ubilab-ws21/puzzle-4/Firmware/Raspberry/pictures/Achtung.png

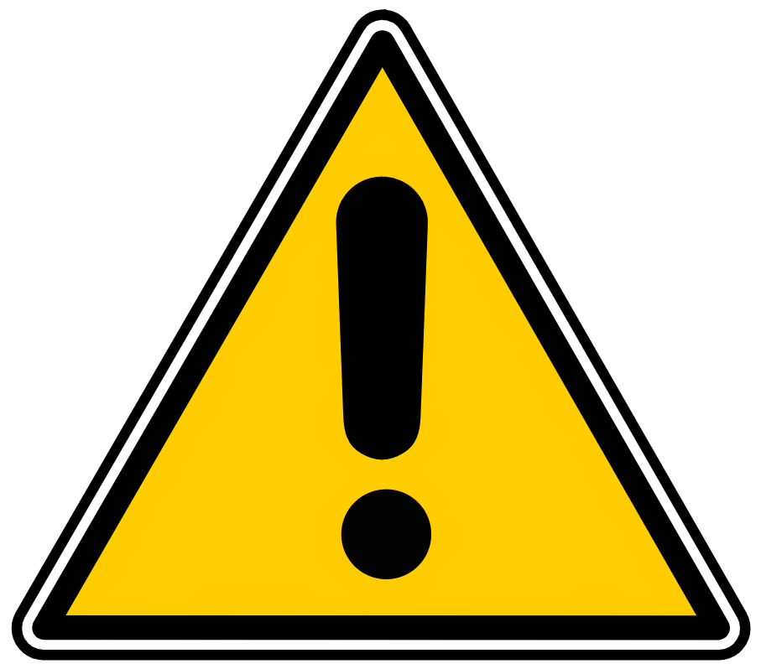
Firmware/Raspberry/pictures/Achtung.png
