ubilab-ws21/puzzle-4/Firmware/Raspberry/pictures/Blitz.png

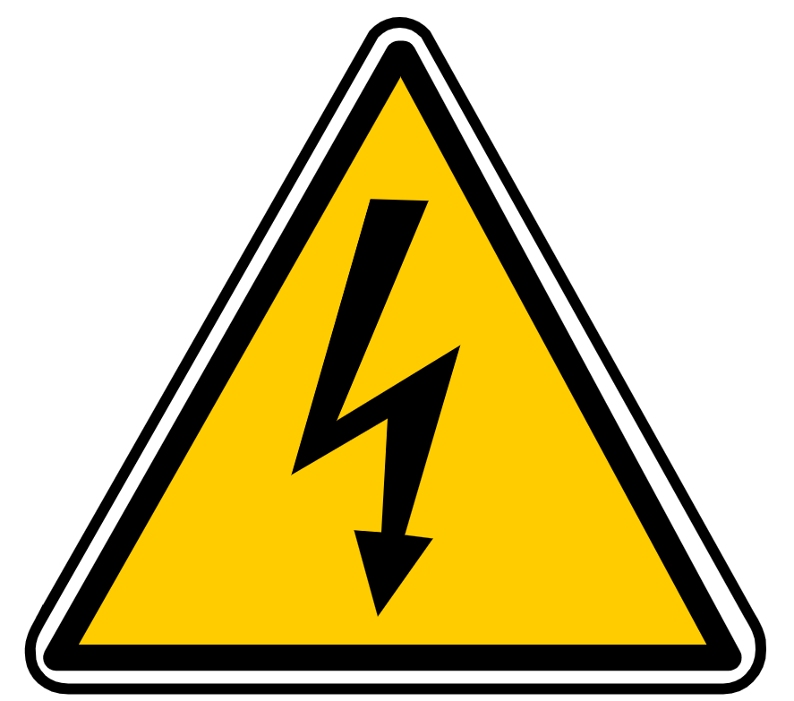
Firmware/Raspberry/pictures/Blitz.png
