ubilab-ws21/puzzle-4/Firmware/Raspberry/pictures/Feuer.png

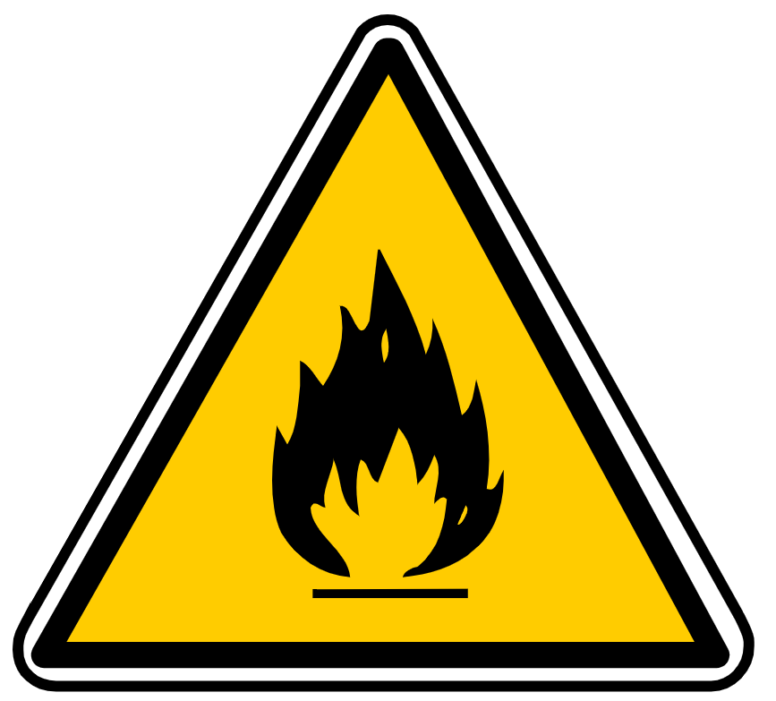
Firmware/Raspberry/pictures/Feuer.png
