ubilab-ws21/puzzle-4/Firmware/Raspberry/progressbar/progress_4.JPG

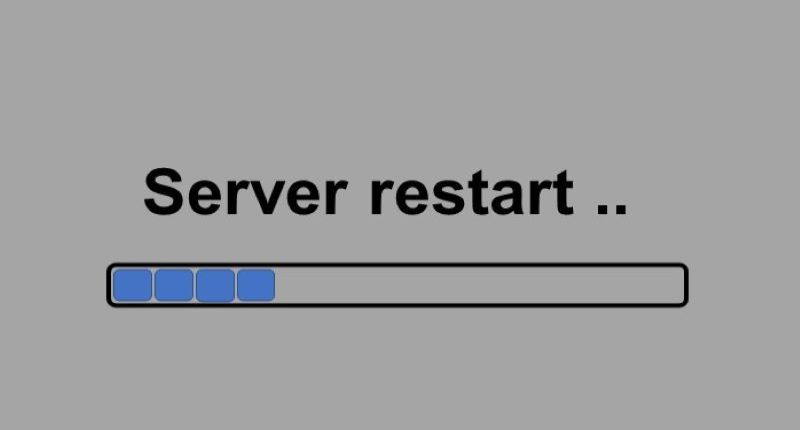
Firmware/Raspberry/progressbar/progress_4.JPG
