ubilab-ws21/puzzle-4/Firmware/Raspberry/progressbar/progress_9.JPG

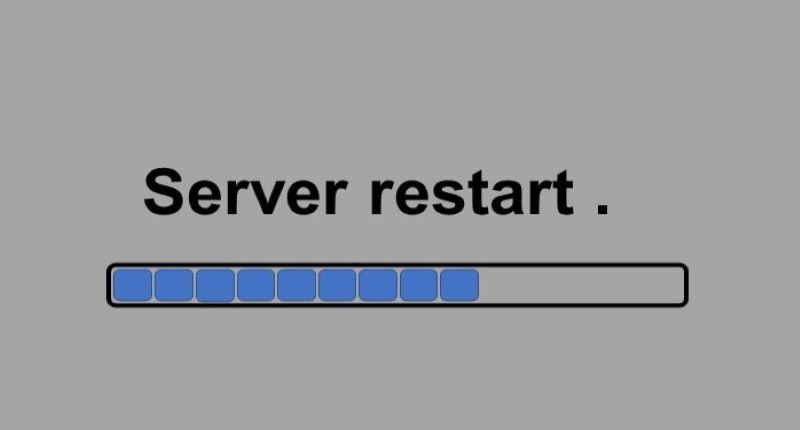
Firmware/Raspberry/progressbar/progress_9.JPG
