ubilab-ws21/puzzle-4/Firmware/Raspberry/sequences/0_1.jpg

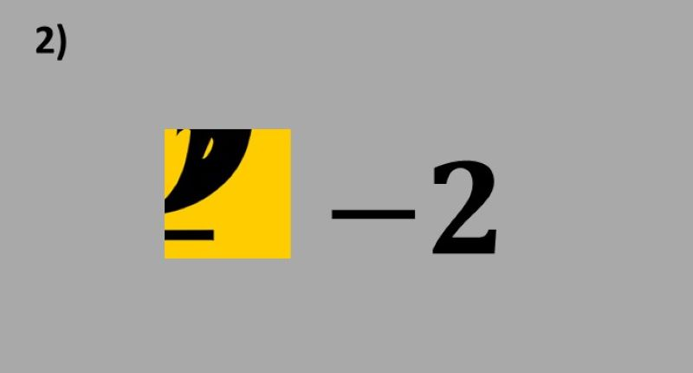
Firmware/Raspberry/sequences/0_1.jpg
