ubilab-ws21/puzzle-4/Firmware/Raspberry/sequences/0_2.jpg

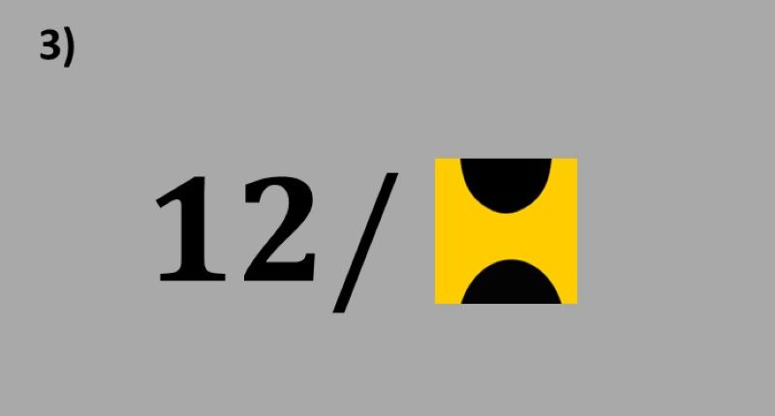
Firmware/Raspberry/sequences/0_2.jpg
