ubilab-ws21/puzzle-4/Firmware/Raspberry/sequences/0_3.jpg

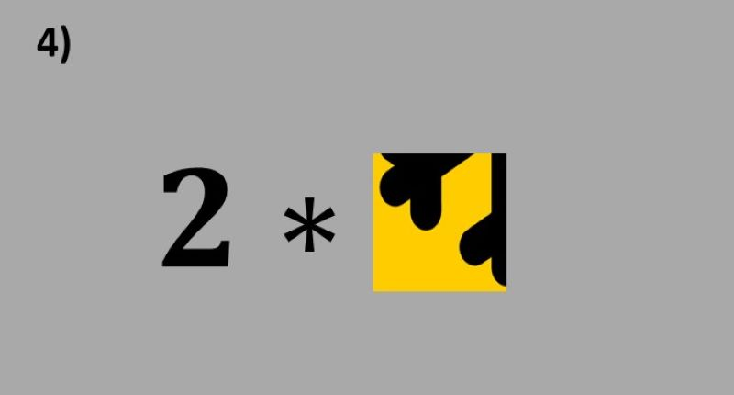
Firmware/Raspberry/sequences/0_3.jpg
