ubilab-ws21/puzzle-4/Firmware/Raspberry/sequences/1_1.jpg

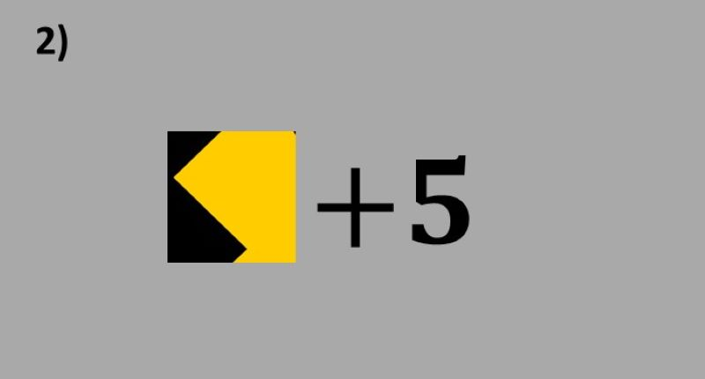
Firmware/Raspberry/sequences/1_1.jpg
