ubilab-ws21/puzzle-4/Firmware/Raspberry/sequences/1_2.jpg

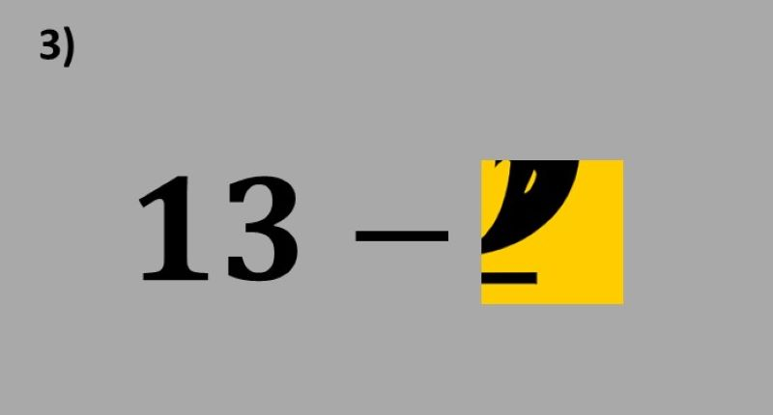
Firmware/Raspberry/sequences/1_2.jpg
