ubilab-ws21/puzzle-4/Firmware/Raspberry/sequences/2_0.jpg

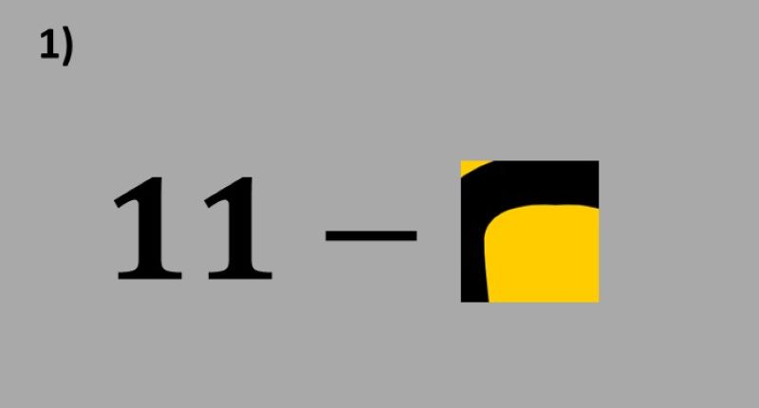
Firmware/Raspberry/sequences/2_0.jpg
