ubilab-ws21/puzzle-4/Firmware/Raspberry/sequences/2_2.jpg

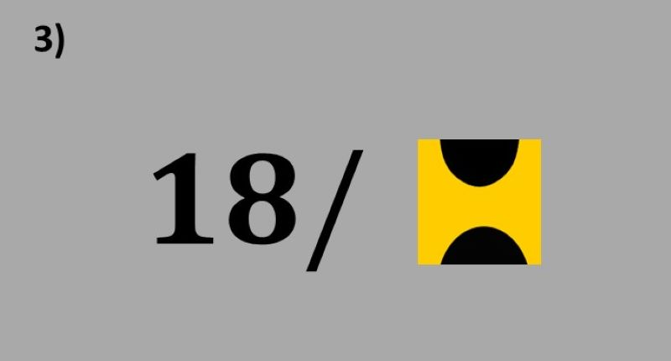
Firmware/Raspberry/sequences/2_2.jpg
