ubilab-ws21/puzzle-4/Firmware/Raspberry/sequences/2_3.jpg

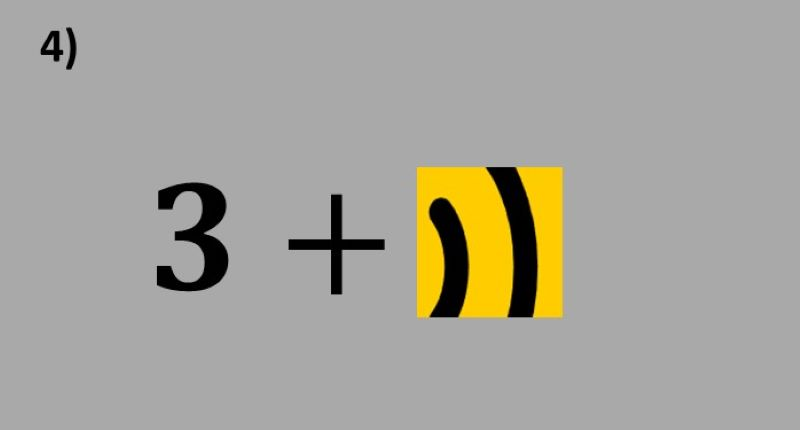
Firmware/Raspberry/sequences/2_3.jpg
