ubilab-ws21/puzzle-4/Firmware/Raspberry/sequences/3_1.jpg

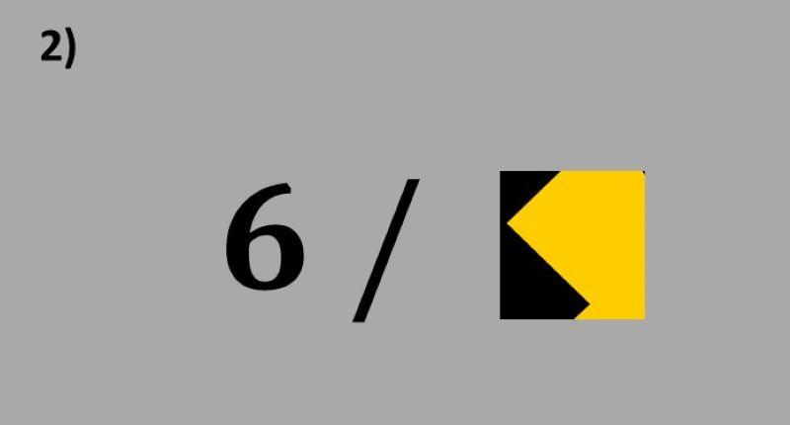
Firmware/Raspberry/sequences/3_1.jpg
