ubilab-ws21/puzzle-4/Firmware/Raspberry/sequences/3_2.jpg

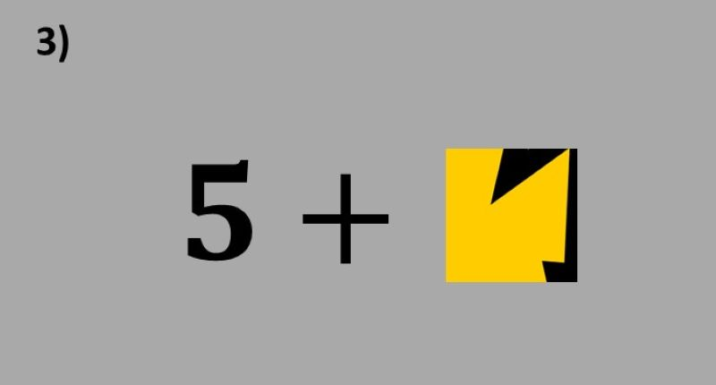
Firmware/Raspberry/sequences/3_2.jpg
