ubilab-ws21/puzzle-4/Firmware/Raspberry/sequences/4_2.JPG

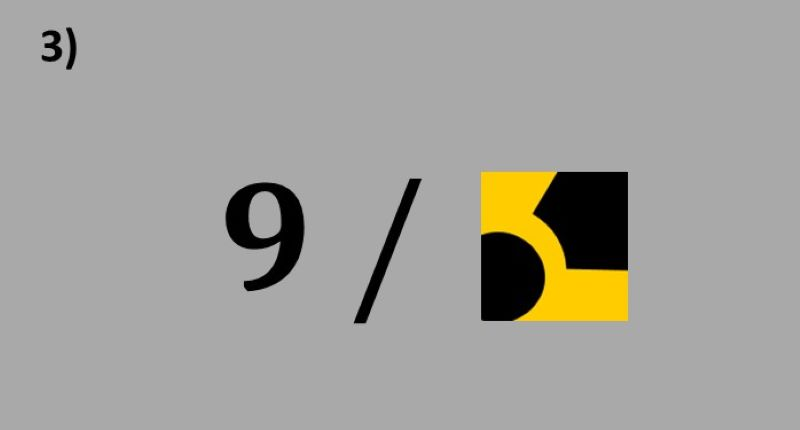
Firmware/Raspberry/sequences/4_2.JPG
