ubilab-ws21/puzzle-4/Firmware/Raspberry/sequences/5_0.JPG

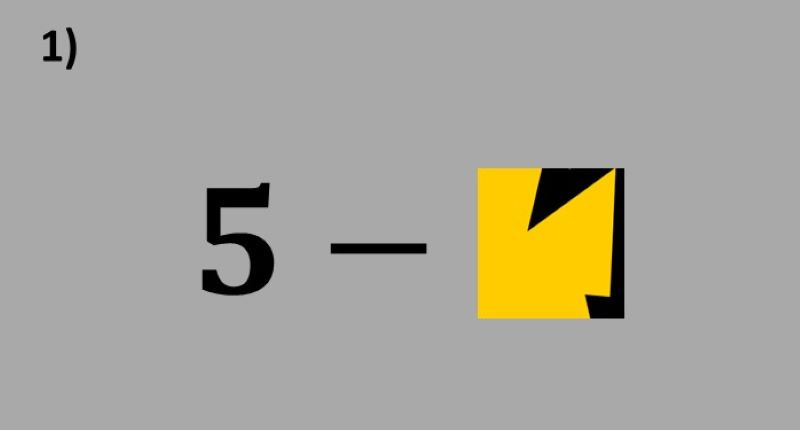
Firmware/Raspberry/sequences/5_0.JPG
