ubilab-ws21/puzzle-4/Firmware/Raspberry/sequences/5_1.JPG

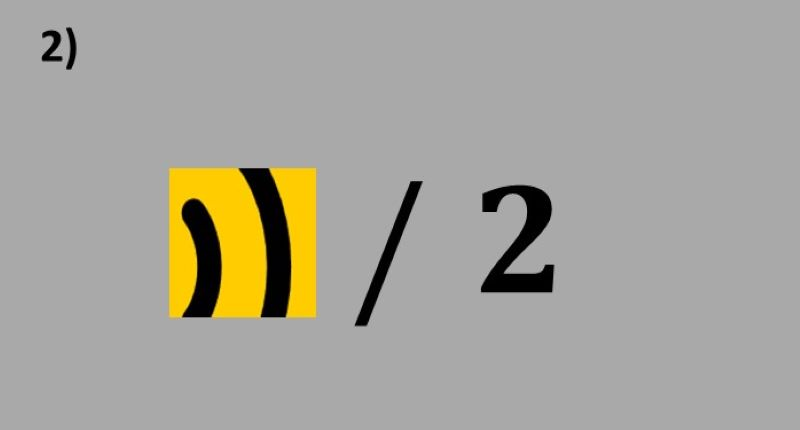
Firmware/Raspberry/sequences/5_1.JPG
