ubilab-ws21/puzzle-4/Firmware/Raspberry/sequences/6_1.JPG

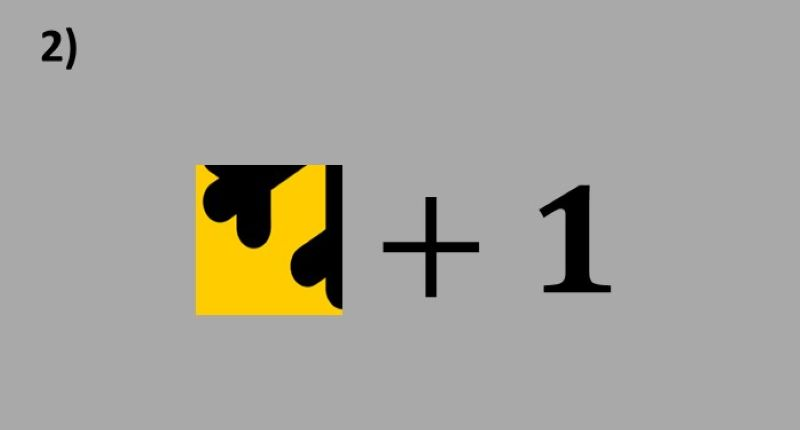
Firmware/Raspberry/sequences/6_1.JPG
