ubilab-ws21/puzzle-4/Firmware/Raspberry/sequences/7_2.JPG

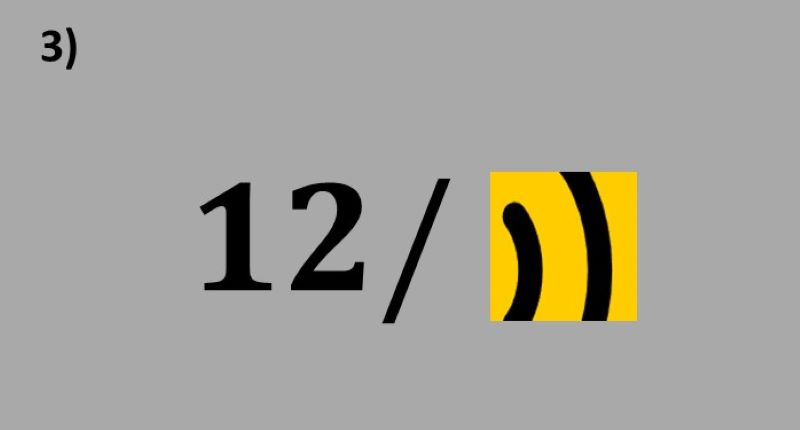
Firmware/Raspberry/sequences/7_2.JPG
