ubilab-ws21/puzzle-4/Firmware/Raspberry/sequences/8_2.JPG

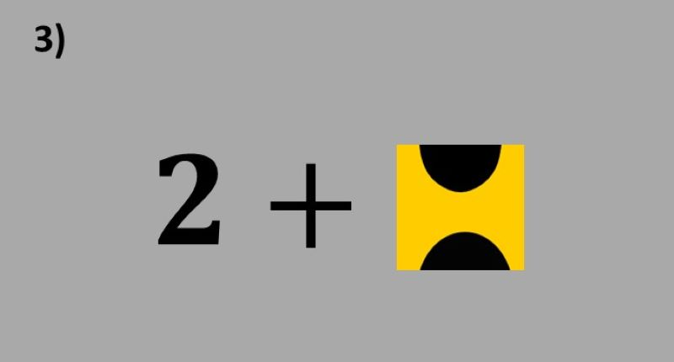
Firmware/Raspberry/sequences/8_2.JPG
