ubilab-ws21/puzzle-4/Firmware/Raspberry/sequences/9_3.JPG

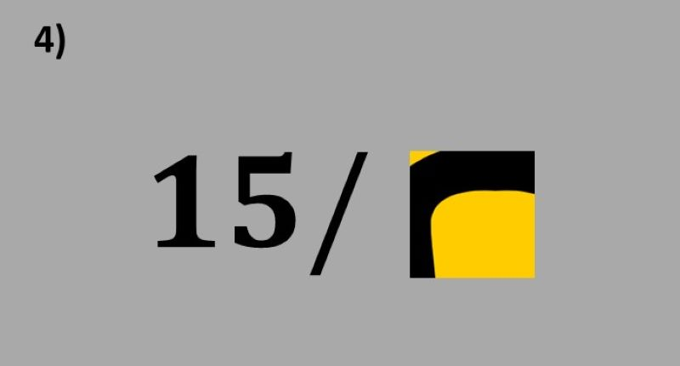
Firmware/Raspberry/sequences/9_3.JPG
