ubilab-ws21/puzzle-4/Firmware/Raspberry/sequences/boot_2.jpg

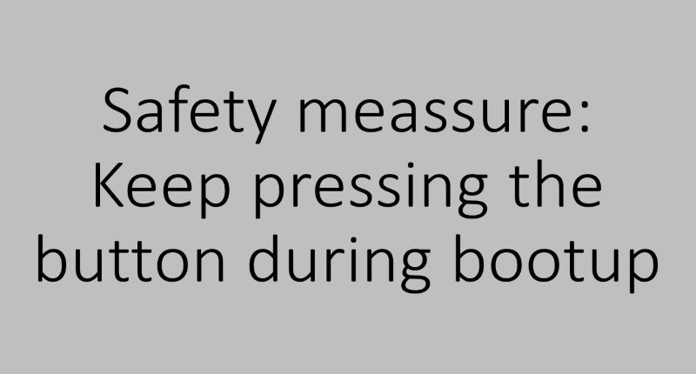
Firmware/Raspberry/sequences/boot_2.jpg
