ubilab-ws21/puzzle-4/Firmware/Raspberry/sequences/boot_3.jpg

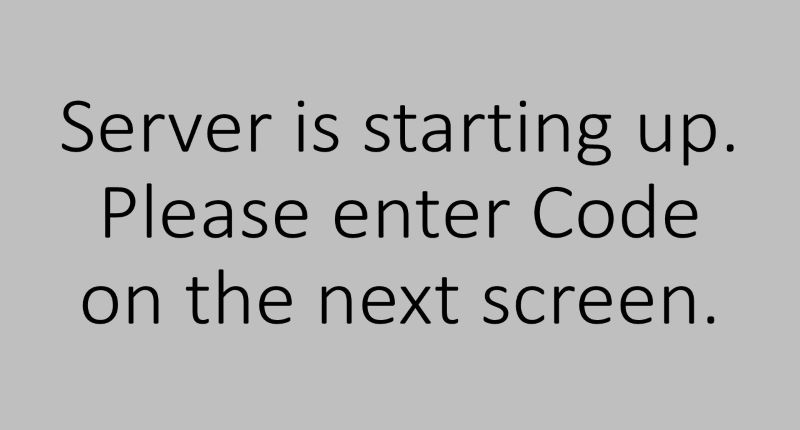
Firmware/Raspberry/sequences/boot_3.jpg
