ubilab-ws21/puzzle-4/Firmware/Raspberry/sequences/Correct.jpg

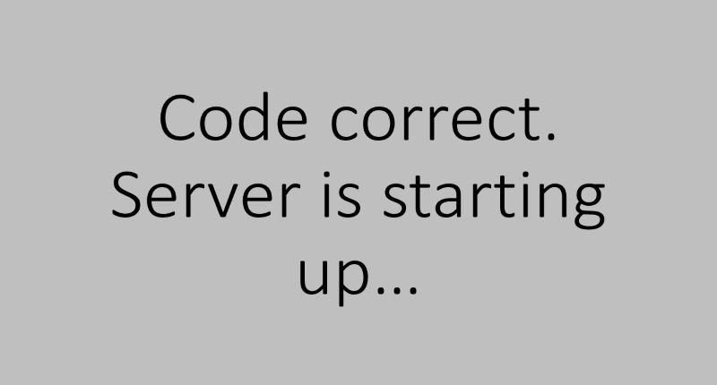
Firmware/Raspberry/sequences/Correct.jpg
