ubilab-ws21/puzzle-4/Firmware/Raspberry/sequences/over.jpg

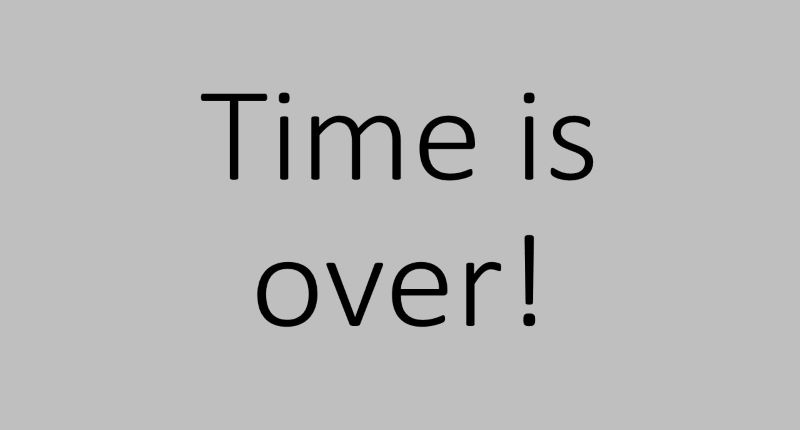
Firmware/Raspberry/sequences/over.jpg
