ubilab-ws21/puzzle-4/Firmware/Raspberry/sequences/Reset.jpg

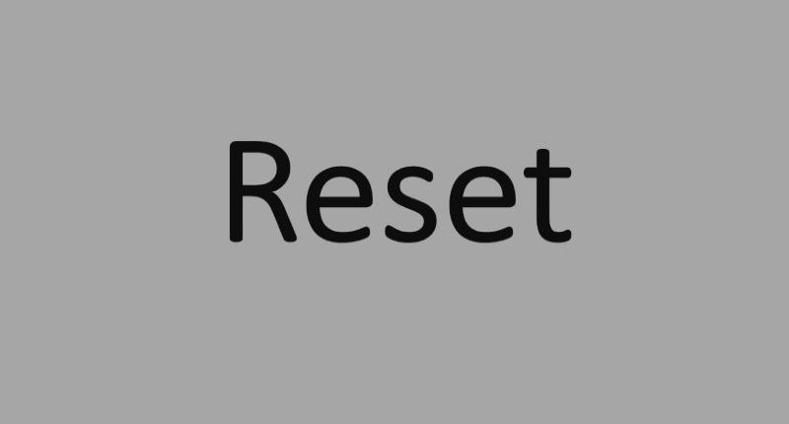
Firmware/Raspberry/sequences/Reset.jpg
