ubilab-ws21/puzzle-4/Firmware/Raspberry/sequences/Restart.jpg

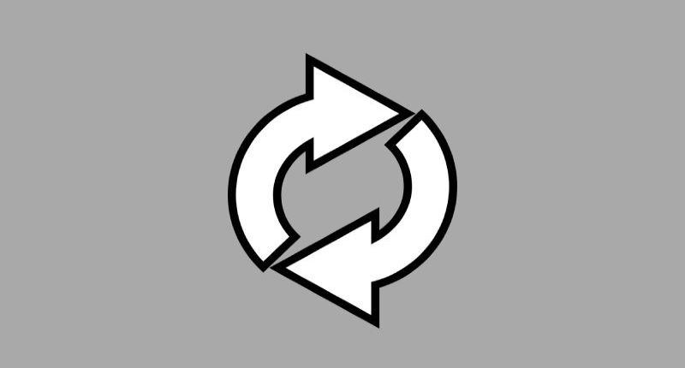
Firmware/Raspberry/sequences/Restart.jpg
