ubilab-ws21/puzzle-4/Firmware/Raspberry/sequences/startup2.jpg

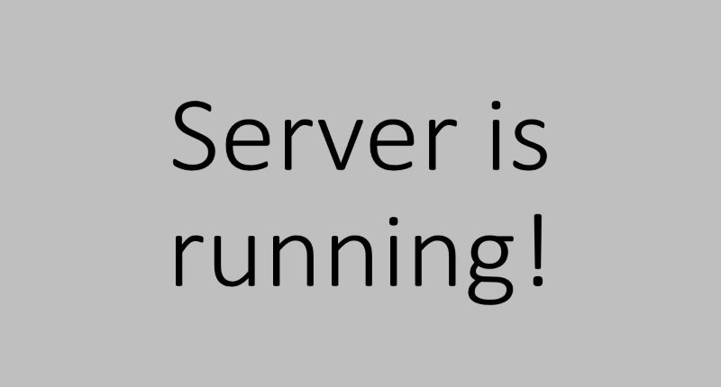
Firmware/Raspberry/sequences/startup2.jpg
