ubilab-ws21/puzzle-4/Firmware/Raspberry/sequences/startup.jpg

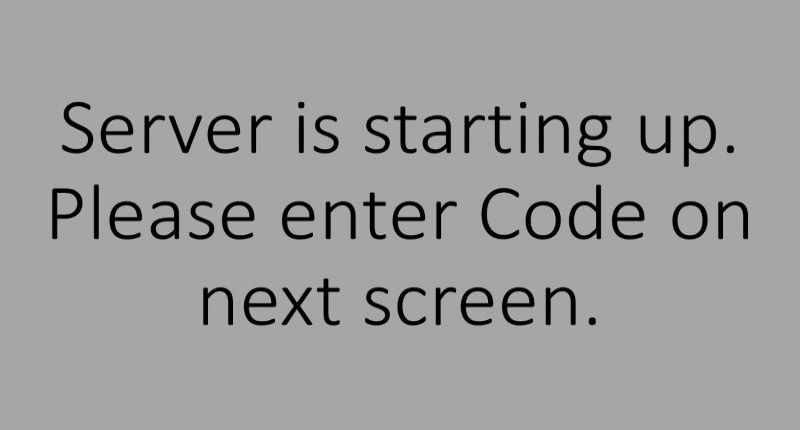
Firmware/Raspberry/sequences/startup.jpg
