ubilab-ws21/puzzle-4/Firmware/Raspberry/sequences/Wrong.jpg

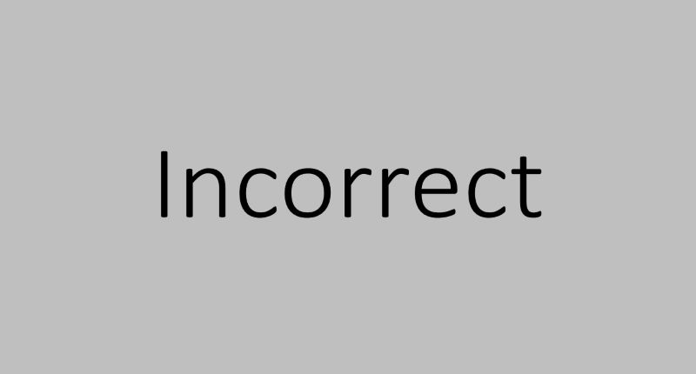
Firmware/Raspberry/sequences/Wrong.jpg
