ubilab-ws21/puzzle-4/Sequences/cheatsheet.jpeg

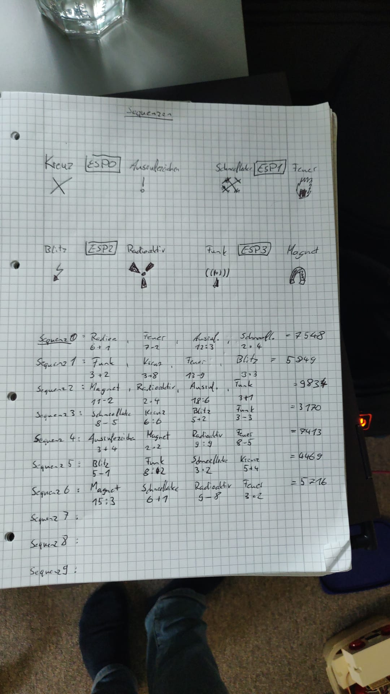
Sequences/cheatsheet.jpeg
