ubilab-ws21/puzzle-4/Sequences/demo-sequence.PNG

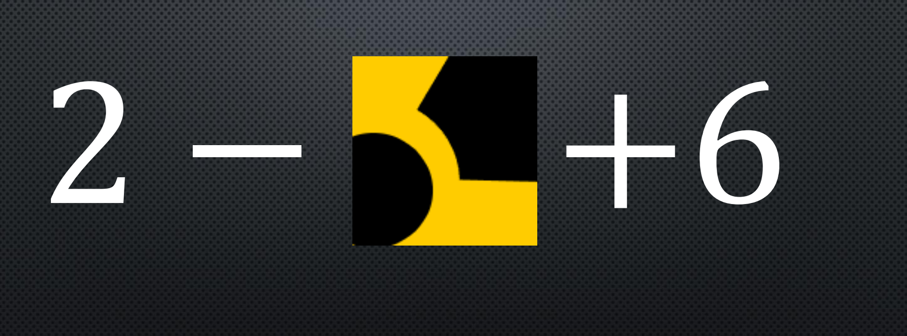
Sequences/demo-sequence.PNG
