ubilab-ws21/puzzle-4/Sequences/demo-sign.png

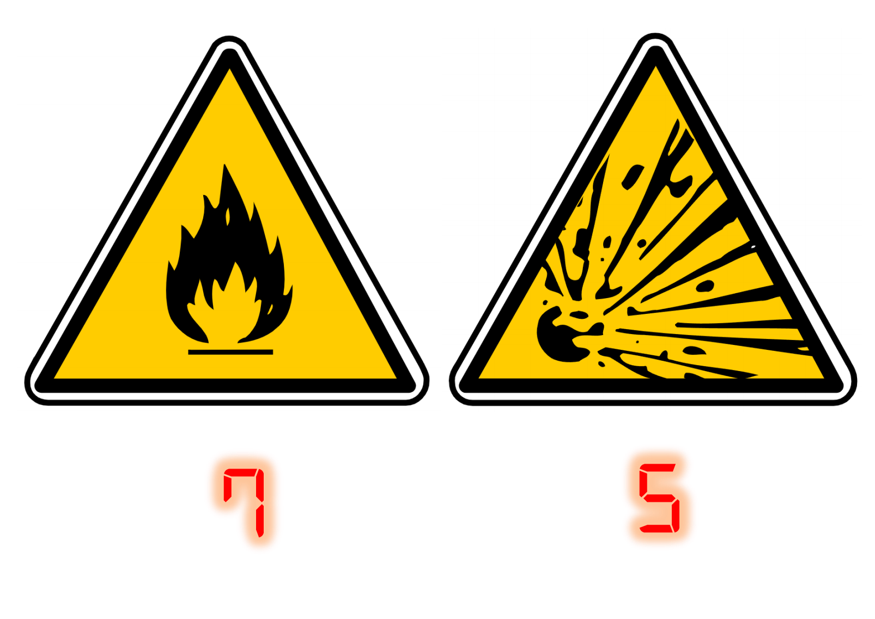
Sequences/demo-sign.png
